MaxMax-embedded/hakadi_soidum_ion_18650/Measurement_Data/static_capacity_tests/static_test_05_1c5-2-3.csv

step | mode | time | voltage | current
0 | 0 | 202 | 4.0783 | 0.1003
1 | 0 | 303 | 4.0731 | -0.0101
1 | 1 | 404 | 4.0824 | 0.1652
1 | 1 | 505 | 4.0789 | 0.1014
1 | 1 | 606 | 4.0813 | 0.1439
1 | 1 | 707 | 4.0830 | 0.1774
1 | 1 | 808 | 4.0849 | 0.2057
1 | 1 | 909 | 4.0864 | 0.2321
1 | 1 | 1010 | 4.0879 | 0.2534
1 | 1 | 1111 | 4.0892 | 0.2807
1 | 1 | 1212 | 4.0903 | 0.2959
1 | 1 | 1313 | 4.0914 | 0.3152
1 | 1 | 1414 | 4.0922 | 0.3233
1 | 1 | 1515 | 4.0933 | 0.3426
1 | 1 | 1616 | 4.0941 | 0.3527
1 | 1 | 1717 | 4.0946 | 0.3709
1 | 1 | 1818 | 4.0954 | 0.3821
1 | 1 | 1920 | 4.0957 | 0.3882
1 | 1 | 2021 | 4.0965 | 0.4014
1 | 1 | 2122 | 4.0967 | 0.3973
1 | 1 | 2223 | 4.0971 | 0.4034
1 | 1 | 2324 | 4.0976 | 0.4135
1 | 1 | 2425 | 4.0980 | 0.4115
1 | 1 | 2526 | 4.0982 | 0.4155
1 | 1 | 2627 | 4.0984 | 0.4267
1 | 1 | 2728 | 4.0988 | 0.4236
1 | 1 | 2829 | 4.0988 | 0.4287
1 | 1 | 2930 | 4.0991 | 0.4267
1 | 1 | 3031 | 4.0991 | 0.4368
1 | 1 | 3132 | 4.0993 | 0.4389
1 | 1 | 3233 | 4.0995 | 0.4297
1 | 1 | 3334 | 4.0997 | 0.4338
1 | 1 | 3435 | 4.0997 | 0.4358
1 | 1 | 3536 | 4.0999 | 0.4378
1 | 1 | 3637 | 4.0999 | 0.4368
1 | 1 | 3738 | 4.0999 | 0.4318
1 | 1 | 3840 | 4.1001 | 0.4358
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
