MaxMax-embedded/hakadi_soidum_ion_18650/Measurement_Data/static_capacity_tests/static_test_05_1c5-3-1.csv

step | mode | time | voltage | current
0 | 0 | 202 | 4.0796 | 0.1014
1 | 0 | 303 | 4.0742 | 0.0041
1 | 1 | 404 | 4.0832 | 0.1824
1 | 1 | 505 | 4.0798 | 0.1064
1 | 1 | 606 | 4.0817 | 0.1409
1 | 1 | 707 | 4.0836 | 0.1733
1 | 1 | 808 | 4.0851 | 0.2057
1 | 1 | 909 | 4.0869 | 0.2331
1 | 1 | 1010 | 4.0879 | 0.2574
1 | 1 | 1111 | 4.0894 | 0.2777
1 | 1 | 1212 | 4.0905 | 0.2949
1 | 1 | 1313 | 4.0914 | 0.3101
1 | 1 | 1414 | 4.0922 | 0.3355
1 | 1 | 1515 | 4.0931 | 0.3385
1 | 1 | 1616 | 4.0941 | 0.3628
1 | 1 | 1717 | 4.0948 | 0.3659
1 | 1 | 1818 | 4.0954 | 0.3791
1 | 1 | 1920 | 4.0957 | 0.3821
1 | 1 | 2021 | 4.0963 | 0.3912
1 | 1 | 2122 | 4.0967 | 0.3953
1 | 1 | 2223 | 4.0971 | 0.4044
1 | 1 | 2324 | 4.0974 | 0.4125
1 | 1 | 2425 | 4.0976 | 0.4074
1 | 1 | 2526 | 4.0982 | 0.4186
1 | 1 | 2627 | 4.0984 | 0.4196
1 | 1 | 2728 | 4.0984 | 0.4318
1 | 1 | 2829 | 4.0986 | 0.4287
1 | 1 | 2930 | 4.0989 | 0.4297
1 | 1 | 3031 | 4.0991 | 0.4267
1 | 1 | 3132 | 4.0993 | 0.4307
1 | 1 | 3233 | 4.0995 | 0.4348
1 | 1 | 3334 | 4.0995 | 0.4328
1 | 1 | 3435 | 4.0997 | 0.4348
1 | 1 | 3536 | 4.0997 | 0.4389
1 | 1 | 3637 | 4.0999 | 0.4378
1 | 1 | 3738 | 4.0999 | 0.4297
1 | 1 | 3840 | 4.0999 | 0.4399
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
