MaxMax-embedded/hakadi_soidum_ion_18650/Measurement_Data/static_capacity_tests/static_test_0c5-1-1.csv

step | mode | time | voltage | current
0 | 0 | 202 | 4.0815 | 0.0983
1 | 0 | 303 | 4.0753 | -0.0051
1 | 1 | 404 | 4.0851 | 0.1662
1 | 1 | 505 | 4.0862 | 0.1784
1 | 1 | 606 | 4.0826 | 0.1135
1 | 1 | 707 | 4.0847 | 0.1459
1 | 1 | 808 | 4.0862 | 0.1733
1 | 1 | 909 | 4.0875 | 0.2027
1 | 1 | 1010 | 4.0890 | 0.2169
1 | 1 | 1111 | 4.0901 | 0.2361
1 | 1 | 1212 | 4.0913 | 0.2605
1 | 1 | 1313 | 4.0922 | 0.2787
1 | 1 | 1414 | 4.0931 | 0.2878
1 | 1 | 1515 | 4.0937 | 0.2929
1 | 1 | 1616 | 4.0946 | 0.3172
1 | 1 | 1717 | 4.0954 | 0.3223
1 | 1 | 1818 | 4.0957 | 0.3284
1 | 1 | 1920 | 4.0963 | 0.3385
1 | 1 | 2021 | 4.0967 | 0.3486
1 | 1 | 2122 | 4.0973 | 0.3497
1 | 1 | 2223 | 4.0976 | 0.3517
1 | 1 | 2324 | 4.0978 | 0.3618
1 | 1 | 2425 | 4.0982 | 0.3720
1 | 1 | 2526 | 4.0984 | 0.3649
1 | 1 | 2627 | 4.0986 | 0.3760
1 | 1 | 2728 | 4.0989 | 0.3709
1 | 1 | 2829 | 4.0989 | 0.3770
1 | 1 | 2930 | 4.0993 | 0.3750
1 | 1 | 3031 | 4.0993 | 0.3791
1 | 1 | 3132 | 4.0995 | 0.3770
1 | 1 | 3233 | 4.0997 | 0.3791
1 | 1 | 3334 | 4.0997 | 0.3841
1 | 1 | 3435 | 4.0997 | 0.3811
1 | 1 | 3536 | 4.0999 | 0.3801
1 | 1 | 3637 | 4.1001 | 0.3831
1 | 1 | 3738 | 4.1001 | 0.3821
1 | 1 | 3840 | 4.0999 | 0.3811
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
