MaxMax-embedded/hakadi_soidum_ion_18650/Measurement_Data/static_capacity_tests/static_test_0c5-2-1.csv

step | mode | time | voltage | current
0 | 0 | 202 | 4.0736 | 0.1064
1 | 0 | 303 | 4.0678 | 0.0081
1 | 1 | 404 | 4.0785 | 0.1986
1 | 1 | 505 | 4.0749 | 0.1277
1 | 1 | 606 | 4.0779 | 0.1845
1 | 1 | 707 | 4.0802 | 0.2209
1 | 1 | 808 | 4.0823 | 0.2595
1 | 1 | 909 | 4.0839 | 0.2899
1 | 1 | 1010 | 4.0856 | 0.3193
1 | 1 | 1111 | 4.0873 | 0.3456
1 | 1 | 1212 | 4.0886 | 0.3679
1 | 1 | 1313 | 4.0897 | 0.3821
1 | 1 | 1414 | 4.0909 | 0.4125
1 | 1 | 1515 | 4.0918 | 0.4206
1 | 1 | 1616 | 4.0929 | 0.4399
1 | 1 | 1717 | 4.0937 | 0.4449
1 | 1 | 1818 | 4.0944 | 0.4551
1 | 1 | 1920 | 4.0950 | 0.4662
1 | 1 | 2021 | 4.0956 | 0.4733
1 | 1 | 2122 | 4.0963 | 0.4885
1 | 1 | 2223 | 4.0965 | 0.4865
1 | 1 | 2324 | 4.0973 | 0.4966
1 | 1 | 2425 | 4.0974 | 0.4997
1 | 1 | 2526 | 4.0980 | 0.5108
1 | 1 | 2627 | 4.0982 | 0.5057
1 | 1 | 2728 | 4.0986 | 0.5149
1 | 1 | 2829 | 4.0986 | 0.5159
1 | 1 | 2930 | 4.0988 | 0.5139
1 | 1 | 3031 | 4.0991 | 0.5169
1 | 1 | 3132 | 4.0991 | 0.5179
1 | 1 | 3233 | 4.0993 | 0.5220
1 | 1 | 3334 | 4.0997 | 0.5240
1 | 1 | 3435 | 4.0997 | 0.5230
1 | 1 | 3536 | 4.0997 | 0.5240
1 | 1 | 3637 | 4.0999 | 0.5280
1 | 1 | 3738 | 4.0999 | 0.5240
1 | 1 | 3840 | 4.1001 | 0.5280
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
