MaxMax-embedded/hakadi_soidum_ion_18650/Measurement_Data/static_capacity_tests/discharge_curve_multiple_c_rates_extended.png

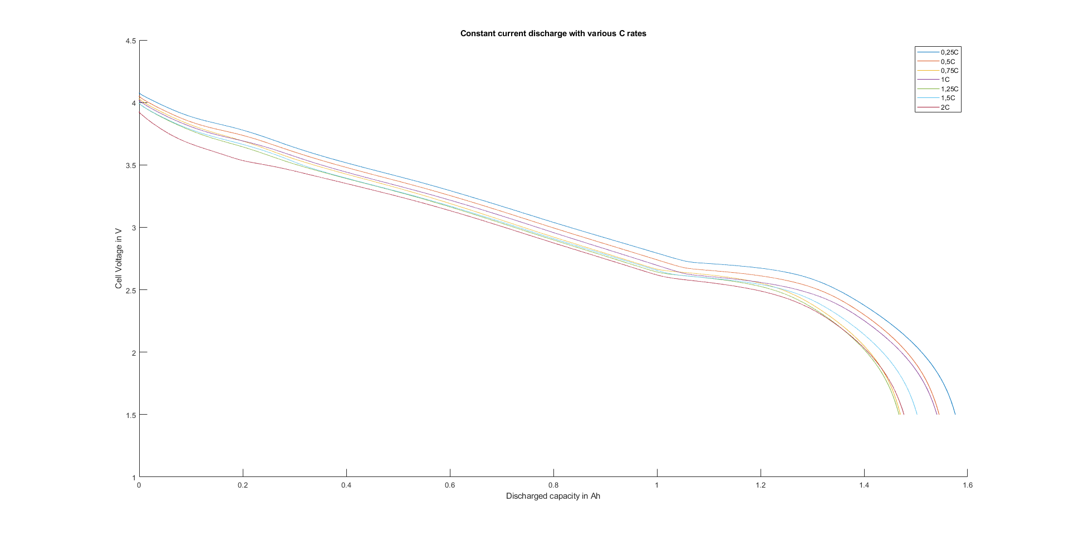
Measurement_Data/static_capacity_tests/discharge_curve_multiple_c_rates_extended.png
