MaxMax-embedded/hakadi_soidum_ion_18650/Hardware/Cell_tester/Cell_tester.kicad_pcb

## KiCad design schem/schem.kicad_sch

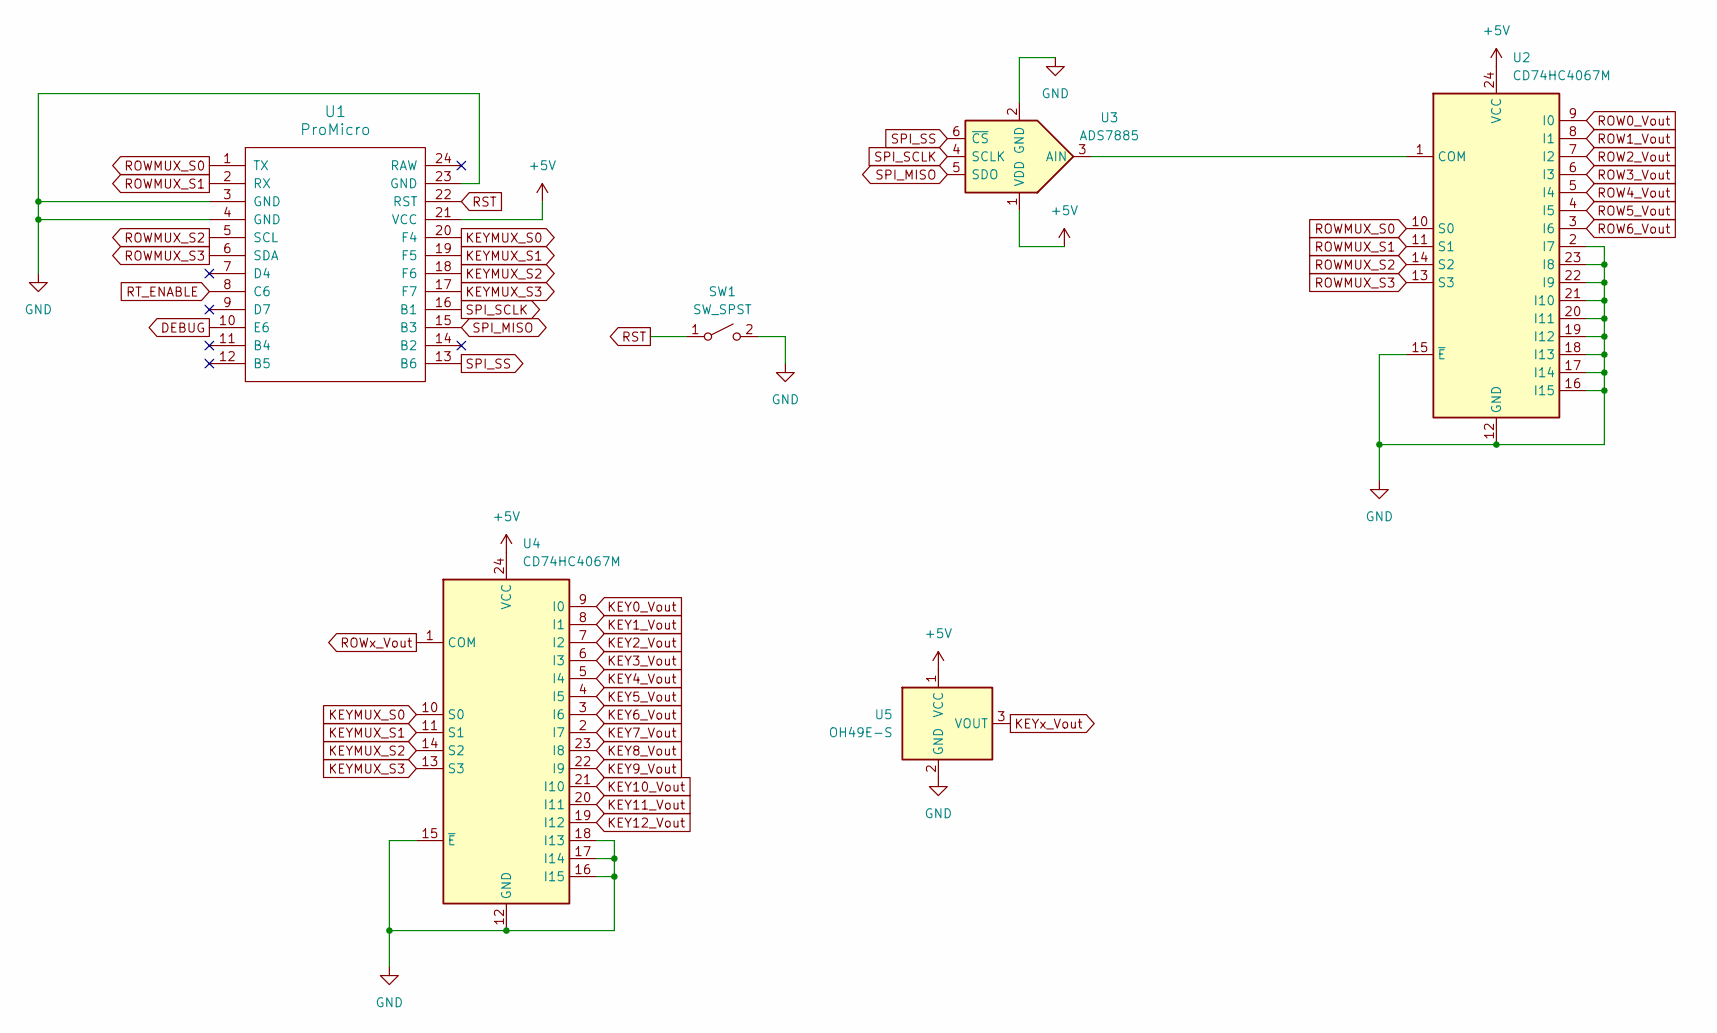
[picture p11: schematic schem.kicad_sch]

Parts:
SW1: SW_SPST
U1: ProMicro
U2, U4: CD74HC4067M; SOIC-24W_7.5x15.4mm_P1.27mm
U3: ADS7885; TSOT-23-6
U5: OH49E-S; Allegro_SIP-3

Connections:
+5V: U1.21 (VCC), U2.24 (VCC), U3.1 (VDD), U4.24 (VCC), U5.1 (VCC)
DEBUG: U1.10 (E6)
GND: SW1.2 (B), U1.3 (GND), U1.4 (GND), U1.23 (GND), U2.2 (I7), U2.12 (GND), U2.15 (~E), U2.16 (I15), U2.17 (I14), U2.18 (I13), U2.19 (I12), U2.20 (I11), U2.21 (I10), U2.22 (I9), U2.23 (I8), U3.2 (GND), U4.12 (GND), U4.15 (~E), U4.16 (I15), U4.17 (I14), U4.18 (I13), U5.2 (GND)
KEY0_Vout: U4.9 (I0)
KEY1_Vout: U4.8 (I1)
KEY2_Vout: U4.7 (I2)
KEY3_Vout: U4.6 (I3)
KEY4_Vout: U4.5 (I4)
KEY5_Vout: U4.4 (I5)
KEY6_Vout: U4.3 (I6)
KEY7_Vout: U4.2 (I7)
KEY8_Vout: U4.23 (I8)
KEY9_Vout: U4.22 (I9)
KEY10_Vout: U4.21 (I10)
KEY11_Vout: U4.20 (I11)
KEY12_Vout: U4.19 (I12)
KEYMUX_S0: U1.20 (F4), U4.10 (S0)
KEYMUX_S1: U1.19 (F5), U4.11 (S1)
KEYMUX_S2: U1.18 (F6), U4.14 (S2)
KEYMUX_S3: U1.17 (F7), U4.13 (S3)
KEYx_Vout: U5.3 (VOUT)
unnamed: U2.1 (COM), U3.3 (AIN)
ROW0_Vout: U2.9 (I0)
ROW1_Vout: U2.8 (I1)
ROW2_Vout: U2.7 (I2)
ROW3_Vout: U2.6 (I3)
ROW4_Vout: U2.5 (I4)
ROW5_Vout: U2.4 (I5)
ROW6_Vout: U2.3 (I6)
ROWMUX_S0: U1.1 (TX), U2.10 (S0)
ROWMUX_S1: U1.2 (RX), U2.11 (S1)
ROWMUX_S2: U1.5 (SCL), U2.14 (S2)
ROWMUX_S3: U1.6 (SDA), U2.13 (S3)
ROWx_Vout: U4.1 (COM)
RST: SW1.1 (A), U1.22 (RST)
RT_ENABLE: U1.8 (C6)
SPI_MISO: U1.15 (B3), U3.5 (SDO)
SPI_SCLK: U1.16 (B1), U3.4 (SCLK)
SPI_SS: U1.13 (B6), U3.6 (~CS)
